buesst1/CDE2_Smart_Classroom/Data_Analysis/Plots/Co2_steigung_0g_2o.png

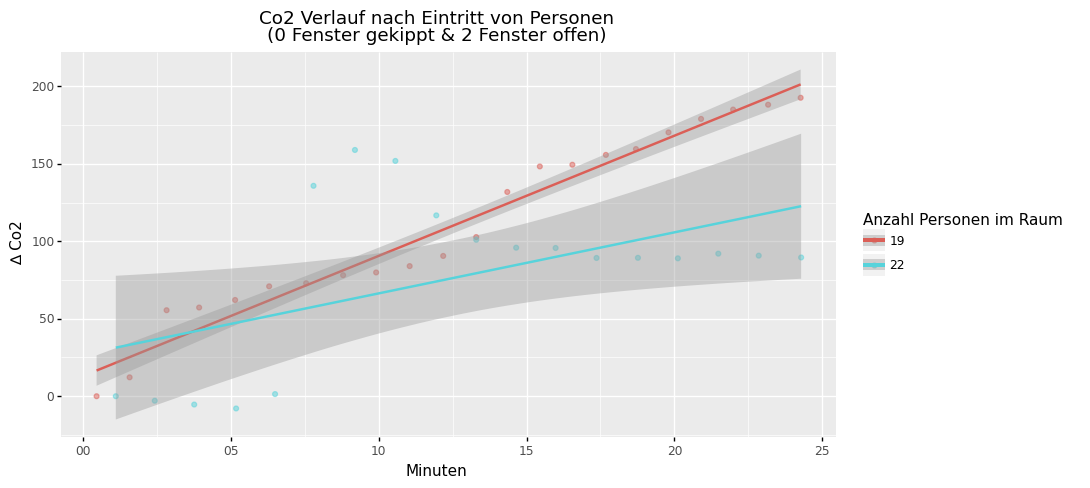
Data_Analysis/Plots/Co2_steigung_0g_2o.png
