buesst1/CDE2_Smart_Classroom/Data_Analysis/Plots/Co2_steigung_2g_1o.png

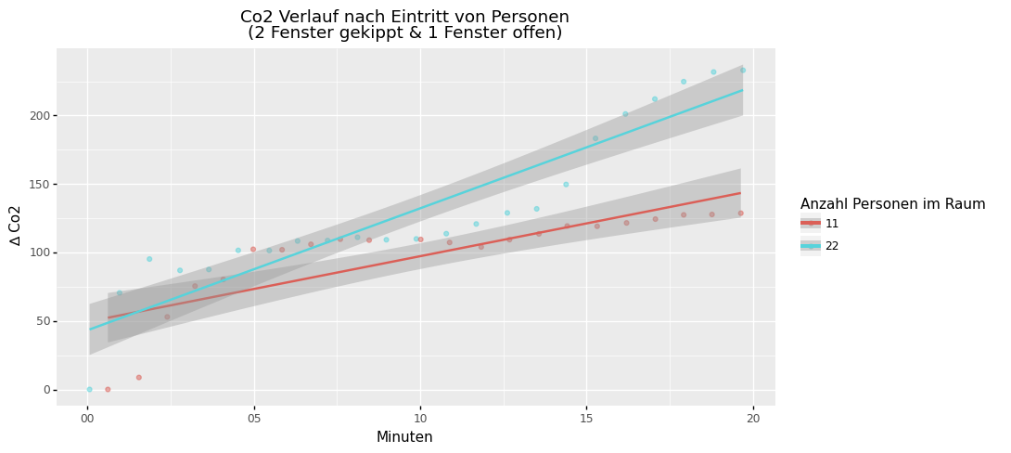
Data_Analysis/Plots/Co2_steigung_2g_1o.png
