buesst1/CDE2_Smart_Classroom/Data_Analysis/Plots/heizenergie.png

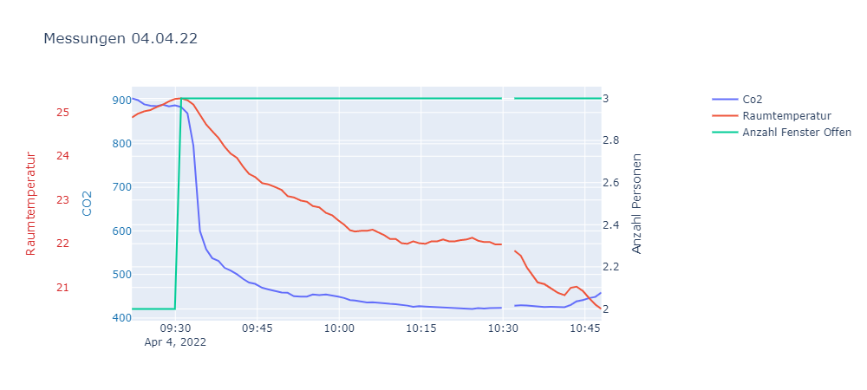
Data_Analysis/Plots/heizenergie.png
