buesst1/CDE2_Smart_Classroom/Data_Analysis/Plots/korrelation luft-co2.png

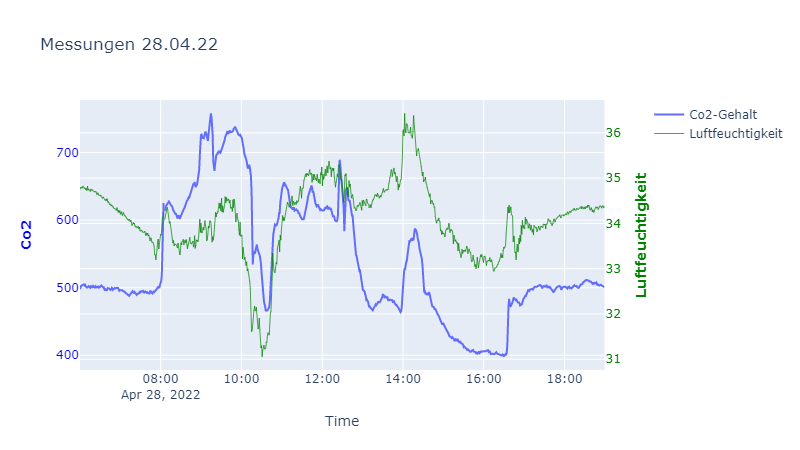
Data_Analysis/Plots/korrelation luft-co2.png
